ifilot/p2000t-video-to-vga-adapter/gui/assets/p2000t-capture-master-v2.png

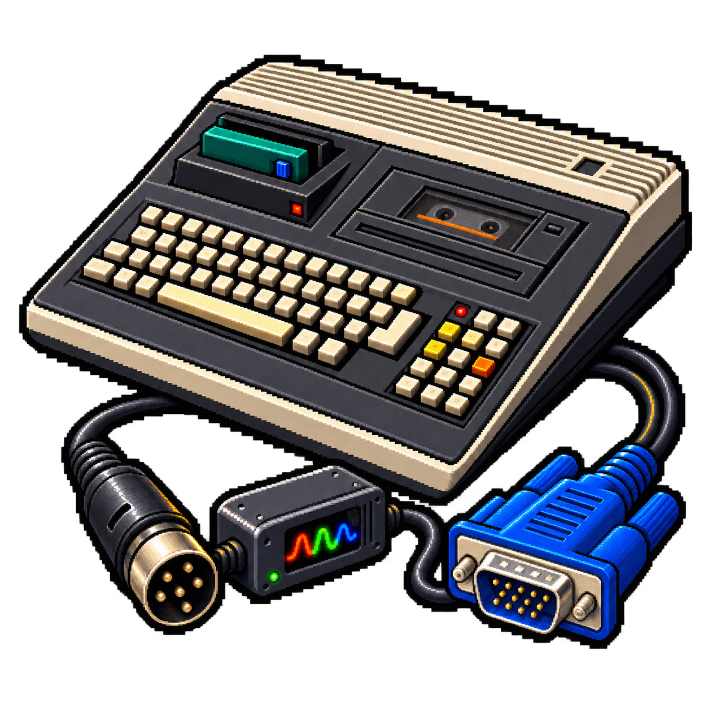
gui/assets/p2000t-capture-master-v2.png
