ifilot/p2000t-video-to-vga-adapter/gui/assets/p2000t-capture-master.png

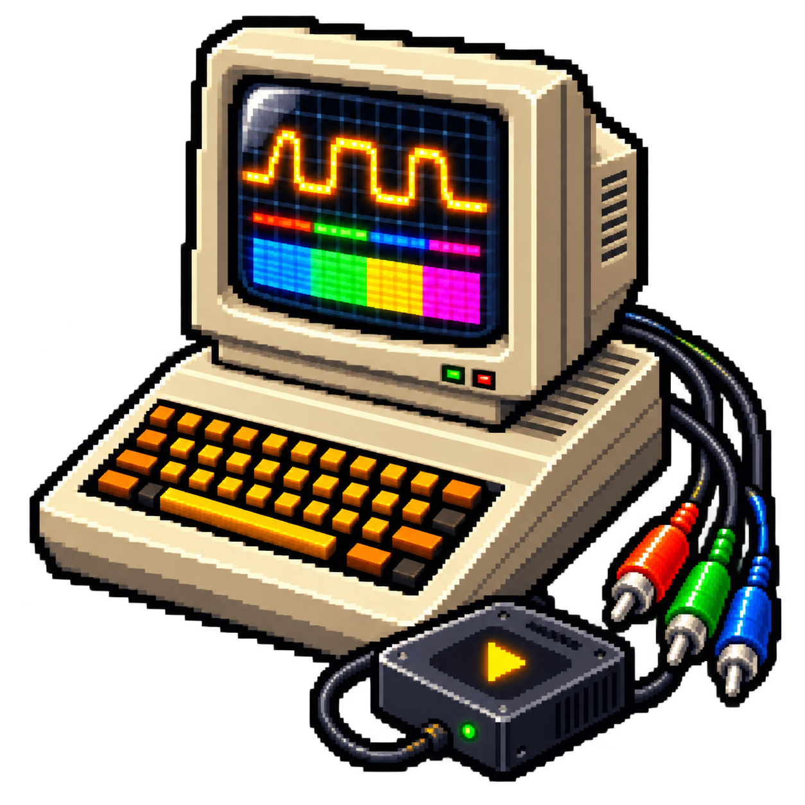
gui/assets/p2000t-capture-master.png
