ifilot/p2000t-video-to-vga-adapter/src/p2000t_diagnostic_protocol.h

/*
 * SPDX-FileCopyrightText: 2026 Ivo Filot <ivo@ivofilot.nl>
 * SPDX-License-Identifier: GPL-3.0-or-later
 */

#ifndef P2000T_DIAGNOSTIC_PROTOCOL_H
#define P2000T_DIAGNOSTIC_PROTOCOL_H

/** Lossless Pico 2 logic-analyzer record format shared with the viewer. */
enum {
    P2000T_DIAGNOSTIC_PROTOCOL_VERSION = 2,
    P2000T_DIAGNOSTIC_HEADER_SIZE = 72,

    P2000T_DIAGNOSTIC_RECORD_SESSION = 1,
    P2000T_DIAGNOSTIC_RECORD_TIMING = 2,
    P2000T_DIAGNOSTIC_RECORD_RAW_RGBS = 3,
    P2000T_DIAGNOSTIC_RECORD_COMPLETE = 4,

    P2000T_DIAGNOSTIC_FLAG_SIGNAL_PRESENT = 1u << 0,
    P2000T_DIAGNOSTIC_FLAG_CANCELLED = 1u << 1,
    P2000T_DIAGNOSTIC_FLAG_WORDS_LITTLE_ENDIAN = 1u << 2,
    P2000T_DIAGNOSTIC_FLAG_SAMPLES_MSB_FIRST = 1u << 3,
    P2000T_DIAGNOSTIC_FLAG_CAPTURE_OVERRUN = 1u << 4,
    P2000T_DIAGNOSTIC_FLAG_PIO_RX_STALL = 1u << 5,

    P2000T_DIAGNOSTIC_TIMING_SAMPLE_RATE_HZ = 63000000,
    P2000T_DIAGNOSTIC_RAW_SAMPLE_RATE_HZ = 252000000,
    P2000T_DIAGNOSTIC_SAMPLES_PER_NOMINAL_LINE = 16128,
    P2000T_DIAGNOSTIC_TIMING_WORD_COUNT = 43320,
    P2000T_DIAGNOSTIC_TIMING_SAMPLE_COUNT =
        P2000T_DIAGNOSTIC_TIMING_WORD_COUNT * 32,
    P2000T_DIAGNOSTIC_TIMING_PAYLOAD_SIZE =
        P2000T_DIAGNOSTIC_TIMING_WORD_COUNT * 4,
    P2000T_DIAGNOSTIC_MAX_LINES = 16,
    P2000T_DIAGNOSTIC_MAX_RAW_SAMPLE_COUNT =
        P2000T_DIAGNOSTIC_MAX_LINES *
        P2000T_DIAGNOSTIC_SAMPLES_PER_NOMINAL_LINE,
    P2000T_DIAGNOSTIC_MAX_RAW_PAYLOAD_SIZE =
        P2000T_DIAGNOSTIC_MAX_RAW_SAMPLE_COUNT / 2,

    P2000T_DIAGNOSTIC_MIN_START_LINE = 1,
    P2000T_DIAGNOSTIC_MAX_START_LINE = 296,
    P2000T_DIAGNOSTIC_MAX_REPETITIONS = 1000,

    P2000T_DIAGNOSTIC_GUARD_DUPLICATE_SIZE = 64,
    P2000T_DIAGNOSTIC_GUARD_MAGIC_SIZE = 8,
    P2000T_DIAGNOSTIC_GUARD_SIZE =
        P2000T_DIAGNOSTIC_GUARD_DUPLICATE_SIZE +
        P2000T_DIAGNOSTIC_GUARD_MAGIC_SIZE,

    P2000T_DIAGNOSTIC_TYPE_OFFSET = 5,
    P2000T_DIAGNOSTIC_FLAGS_OFFSET = 8,
    P2000T_DIAGNOSTIC_RECORD_SEQUENCE_OFFSET = 12,
    P2000T_DIAGNOSTIC_PAYLOAD_SIZE_OFFSET = 16,
    P2000T_DIAGNOSTIC_CRC32_OFFSET = 20,
    P2000T_DIAGNOSTIC_SESSION_ID_OFFSET = 24,
    P2000T_DIAGNOSTIC_SAMPLE_RATE_OFFSET = 28,
    P2000T_DIAGNOSTIC_SAMPLE_COUNT_OFFSET = 32,
    P2000T_DIAGNOSTIC_START_LINE_OFFSET = 36,
    P2000T_DIAGNOSTIC_LINE_COUNT_OFFSET = 38,
    P2000T_DIAGNOSTIC_REPETITION_OFFSET = 40,
    P2000T_DIAGNOSTIC_REPETITIONS_OFFSET = 42,
    P2000T_DIAGNOSTIC_SAMPLES_PER_LINE_OFFSET = 44,
    P2000T_DIAGNOSTIC_BITS_PER_SAMPLE_OFFSET = 46,
    P2000T_DIAGNOSTIC_SYNC_CHANNEL_OFFSET = 47,
    P2000T_DIAGNOSTIC_FIRST_VISIBLE_OFFSET = 48,
    P2000T_DIAGNOSTIC_HORIZONTAL_OFFSET = 50,
    P2000T_DIAGNOSTIC_PHASE_OFFSET = 52,
    P2000T_DIAGNOSTIC_ODD_PHASE_OFFSET = 54,
    P2000T_DIAGNOSTIC_RATE_TRIM_OFFSET = 56,
    P2000T_DIAGNOSTIC_CHANNEL_MAP_OFFSET = 58,
    P2000T_DIAGNOSTIC_CAPTURE_SEQUENCE_OFFSET = 60,
    P2000T_DIAGNOSTIC_CAPTURE_DURATION_OFFSET = 64,
    P2000T_DIAGNOSTIC_EXPECTED_DURATION_OFFSET = 68,
};

#define P2000T_DIAGNOSTIC_MAGIC "P2DG"
#define P2000T_DIAGNOSTIC_GUARD_MAGIC "P2TAIL!!"

#endif
