ifilot/p2000t-video-to-vga-adapter/src/p2000t_no_signal_layout.h

/*
 * SPDX-FileCopyrightText: 2026 Ivo Filot <ivo@ivofilot.nl>
 * SPDX-License-Identifier: GPL-3.0-or-later
 */

#ifndef P2000T_NO_SIGNAL_LAYOUT_H
#define P2000T_NO_SIGNAL_LAYOUT_H

/**
 * @file p2000t_no_signal_layout.h
 * @brief Shared pixel-exact no-connection overlay layout and bitmap font.
 */

#include <stdint.h>

enum {
    NO_SIGNAL_GLYPH_WIDTH = 5,
    NO_SIGNAL_GLYPH_HEIGHT = 7,
    NO_SIGNAL_FONT_GLYPHS = 36,
    NO_SIGNAL_TITLE_TOP = 3,
    NO_SIGNAL_VERSION_TOP = 13,
    NO_SIGNAL_ICON_TOP = 196,
    NO_SIGNAL_ICON_HEIGHT = 14,
    NO_SIGNAL_STATUS_TOP = 217,
};

#define P2000T_NO_SIGNAL_TITLE "P2000T VID2VGA"
#define P2000T_NO_SIGNAL_VERSION_PREFIX "VERSION "
#define P2000T_NO_SIGNAL_STATUS "NO CONNECTION"

/** Five-bit rows for uppercase letters A-Z followed by digits 0-9. */
static const uint8_t
    p2000t_no_signal_font[NO_SIGNAL_FONT_GLYPHS][NO_SIGNAL_GLYPH_HEIGHT] = {
        {0x0e, 0x11, 0x11, 0x1f, 0x11, 0x11, 0x11}, // A
        {0x1e, 0x11, 0x11, 0x1e, 0x11, 0x11, 0x1e}, // B
        {0x0e, 0x11, 0x10, 0x10, 0x10, 0x11, 0x0e}, // C
        {0x1e, 0x11, 0x11, 0x11, 0x11, 0x11, 0x1e}, // D
        {0x1f, 0x10, 0x10, 0x1e, 0x10, 0x10, 0x1f}, // E
        {0x1f, 0x10, 0x10, 0x1e, 0x10, 0x10, 0x10}, // F
        {0x0e, 0x11, 0x10, 0x17, 0x11, 0x11, 0x0e}, // G
        {0x11, 0x11, 0x11, 0x1f, 0x11, 0x11, 0x11}, // H
        {0x1f, 0x04, 0x04, 0x04, 0x04, 0x04, 0x1f}, // I
        {0x07, 0x02, 0x02, 0x02, 0x12, 0x12, 0x0c}, // J
        {0x11, 0x12, 0x14, 0x18, 0x14, 0x12, 0x11}, // K
        {0x10, 0x10, 0x10, 0x10, 0x10, 0x10, 0x1f}, // L
        {0x11, 0x1b, 0x15, 0x15, 0x11, 0x11, 0x11}, // M
        {0x11, 0x19, 0x15, 0x13, 0x11, 0x11, 0x11}, // N
        {0x0e, 0x11, 0x11, 0x11, 0x11, 0x11, 0x0e}, // O
        {0x1e, 0x11, 0x11, 0x1e, 0x10, 0x10, 0x10}, // P
        {0x0e, 0x11, 0x11, 0x11, 0x15, 0x12, 0x0d}, // Q
        {0x1e, 0x11, 0x11, 0x1e, 0x14, 0x12, 0x11}, // R
        {0x0e, 0x10, 0x10, 0x0e, 0x01, 0x01, 0x1e}, // S
        {0x1f, 0x04, 0x04, 0x04, 0x04, 0x04, 0x04}, // T
        {0x11, 0x11, 0x11, 0x11, 0x11, 0x11, 0x0e}, // U
        {0x11, 0x11, 0x11, 0x11, 0x11, 0x0a, 0x04}, // V
        {0x11, 0x11, 0x11, 0x15, 0x15, 0x1b, 0x11}, // W
        {0x11, 0x0a, 0x04, 0x04, 0x04, 0x0a, 0x11}, // X
        {0x11, 0x0a, 0x04, 0x04, 0x04, 0x04, 0x04}, // Y
        {0x1f, 0x01, 0x02, 0x04, 0x08, 0x10, 0x1f}, // Z
        {0x0e, 0x11, 0x13, 0x15, 0x19, 0x11, 0x0e}, // 0
        {0x04, 0x0c, 0x04, 0x04, 0x04, 0x04, 0x0e}, // 1
        {0x0e, 0x11, 0x01, 0x02, 0x04, 0x08, 0x1f}, // 2
        {0x1e, 0x01, 0x01, 0x0e, 0x01, 0x01, 0x1e}, // 3
        {0x02, 0x06, 0x0a, 0x12, 0x1f, 0x02, 0x02}, // 4
        {0x1f, 0x10, 0x10, 0x1e, 0x01, 0x01, 0x1e}, // 5
        {0x0e, 0x10, 0x10, 0x1e, 0x11, 0x11, 0x0e}, // 6
        {0x1f, 0x01, 0x02, 0x04, 0x08, 0x08, 0x08}, // 7
        {0x0e, 0x11, 0x11, 0x0e, 0x11, 0x11, 0x0e}, // 8
        {0x0e, 0x11, 0x11, 0x0f, 0x01, 0x01, 0x0e}, // 9
};

/** Return one row from the shared five-by-seven firmware font. */
static inline uint8_t p2000t_no_signal_glyph_row(char character,
                                                  unsigned row) {
    if (row >= NO_SIGNAL_GLYPH_HEIGHT) {
        return 0u;
    }
    if (character >= 'A' && character <= 'Z') {
        return p2000t_no_signal_font[(unsigned)(character - 'A')][row];
    }
    if (character >= '0' && character <= '9') {
        return p2000t_no_signal_font[26u + (unsigned)(character - '0')][row];
    }
    return character == '.' && row == 6u ? 0x04u : 0x00u;
}

#endif
